fflori4n/ESP_tankLevelSensor/ESP32_tankLevelSensor/lutFreqTransform.h

double lut1Outputmms = 0;
double lut2Outputmms = 0;
const double freq2mmsLUT[] = {
15000  , 8000  ,
16700 , 7184  ,
16700 , 7168  ,
16700 , 7152  ,
16710 , 7136  ,
16700 , 7120  ,
16450 , 7104  ,
16460 , 7088  ,
16450 , 7071  ,
16450 , 7055  ,
16480 , 7039  ,
16540 , 7023  ,
16600 , 7007  ,
16650 , 6991  ,
16720 , 6975  ,
16810 , 6959  ,
16920 , 6943  ,
17170 , 6927  ,
17250 , 6911  ,
17320 , 6895  ,
17400 , 6879  ,
17480 , 6863  ,
17540 , 6846  ,
17630 , 6830  ,
17720 , 6814  ,
17780 , 6798  ,
17880 , 6782  ,
17960 , 6766  ,
18040 , 6750  ,
18140 , 6734  ,
18260 , 6718  ,
18390 , 6702  ,
18600 , 6686  ,
18740 , 6670  ,
18860 , 6654  ,
18920 , 6638  ,
18950 , 6621  ,
18990 , 6605  ,
19010 , 6589  ,
19070 , 6573  ,
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
 
};
const double mms2correctedmmsLUT[] = {
  3200 , 0 ,
  3450, 50  ,
  3725 , 100 ,
  3970 , 150 ,
  4210 , 200 ,
  4420 , 250 ,
  4650 , 300 ,
  4830 , 350 ,
  5020 , 400 ,
  5220 , 450 ,
  5400 , 500 ,
  5570 , 550 ,
  5740 , 600 ,
  5900 , 650 ,
  6070 , 700 ,
  6220 , 750 ,
  6380 , 800 ,
  6580 , 850 ,
  6720 , 900 ,
  6855 , 950 ,
  6930 , 1000,
  6950,1040
};

double getLUTmms(double in, const bool correction, bool verboseFlag = true) {
  double out = -999;

  if ( in < 1) {      /// if sensor reads 0Hz, probe is not connected or faulty, return error
    return -999;      /// return negative num. to signal no con error - TODO: handle this in liquidLevel.h
  }

  int lutLen = sizeof(freq2mmsLUT) / sizeof(freq2mmsLUT[0]);

  if (in >= freq2mmsLUT[(lutLen - 2)]) { /// check if LUT contains in
    out = freq2mmsLUT[(lutLen - 1)];
  } else if (in < freq2mmsLUT[0]) {
    out = freq2mmsLUT[1];
  } else {
    for (int i = 0; i < lutLen - 2; i += 2) {                               /// Loop over LUT, get two points next to each other
      if (in > freq2mmsLUT[i] && in <= freq2mmsLUT[ i + 2 ]) {               /// if measured value is between the two points
        double percent = (in - freq2mmsLUT[i]) / (freq2mmsLUT[i + 2] - freq2mmsLUT[i]);
        out = freq2mmsLUT[ i + 1 ] + ((freq2mmsLUT[ i + 3 ] - freq2mmsLUT[ i + 1 ]) * percent);
        break;
      }
    }
  }

  if (!correction) {
    if (verboseFlag) {
      Serial.println("Freq -> mm's");
      Serial.print("Freq:\t\t");
      Serial.print(in);
      Serial.print(" LUT Out:\t\t");
      Serial.println(out);
    }

    return out;
  }

  if (verboseFlag) {
      Serial.println("Freq -> mm's");
      Serial.print("Freq:\t\t");
      Serial.print(in);
      Serial.print(" LUT Out:\t\t");
      Serial.println(out);
  }
  lut1Outputmms = out;
  in=out;
  lutLen = sizeof(mms2correctedmmsLUT) / sizeof(mms2correctedmmsLUT[0]);

  if (in >= mms2correctedmmsLUT[(lutLen - 2)]) { /// check if LUT contains in
    out = mms2correctedmmsLUT[(lutLen - 1)];
  } else if (in < mms2correctedmmsLUT[0]) {
    out = mms2correctedmmsLUT[1];
  } else {
    for (int i = 0; i < lutLen - 2; i += 2) {                               /// Loop over LUT, get two points next to each other
      if (in > mms2correctedmmsLUT[i] && in <= mms2correctedmmsLUT[ i + 2 ]) {               /// if measured value is between the two points
        double percent = (in - mms2correctedmmsLUT[i]) / (mms2correctedmmsLUT[i + 2] - mms2correctedmmsLUT[i]);
        out = mms2correctedmmsLUT[ i + 1 ] + ((mms2correctedmmsLUT[ i + 3 ] - mms2correctedmmsLUT[ i + 1 ]) * percent);
        break;
      }
    }
  }

  if (verboseFlag) {
      Serial.println("mm's -> corrected");
      Serial.print("mm:\t\t");
      Serial.print(in);
      Serial.print(" LUT Out:\t\t");
      Serial.println(out);
  }

  lut2Outputmms = out;
  return out;
}
